Ross0907/pompyboard/pcb/pompyboard.kicad_sch

## KiCad design pcb/pompyboard.kicad_sch (2025-07-24)

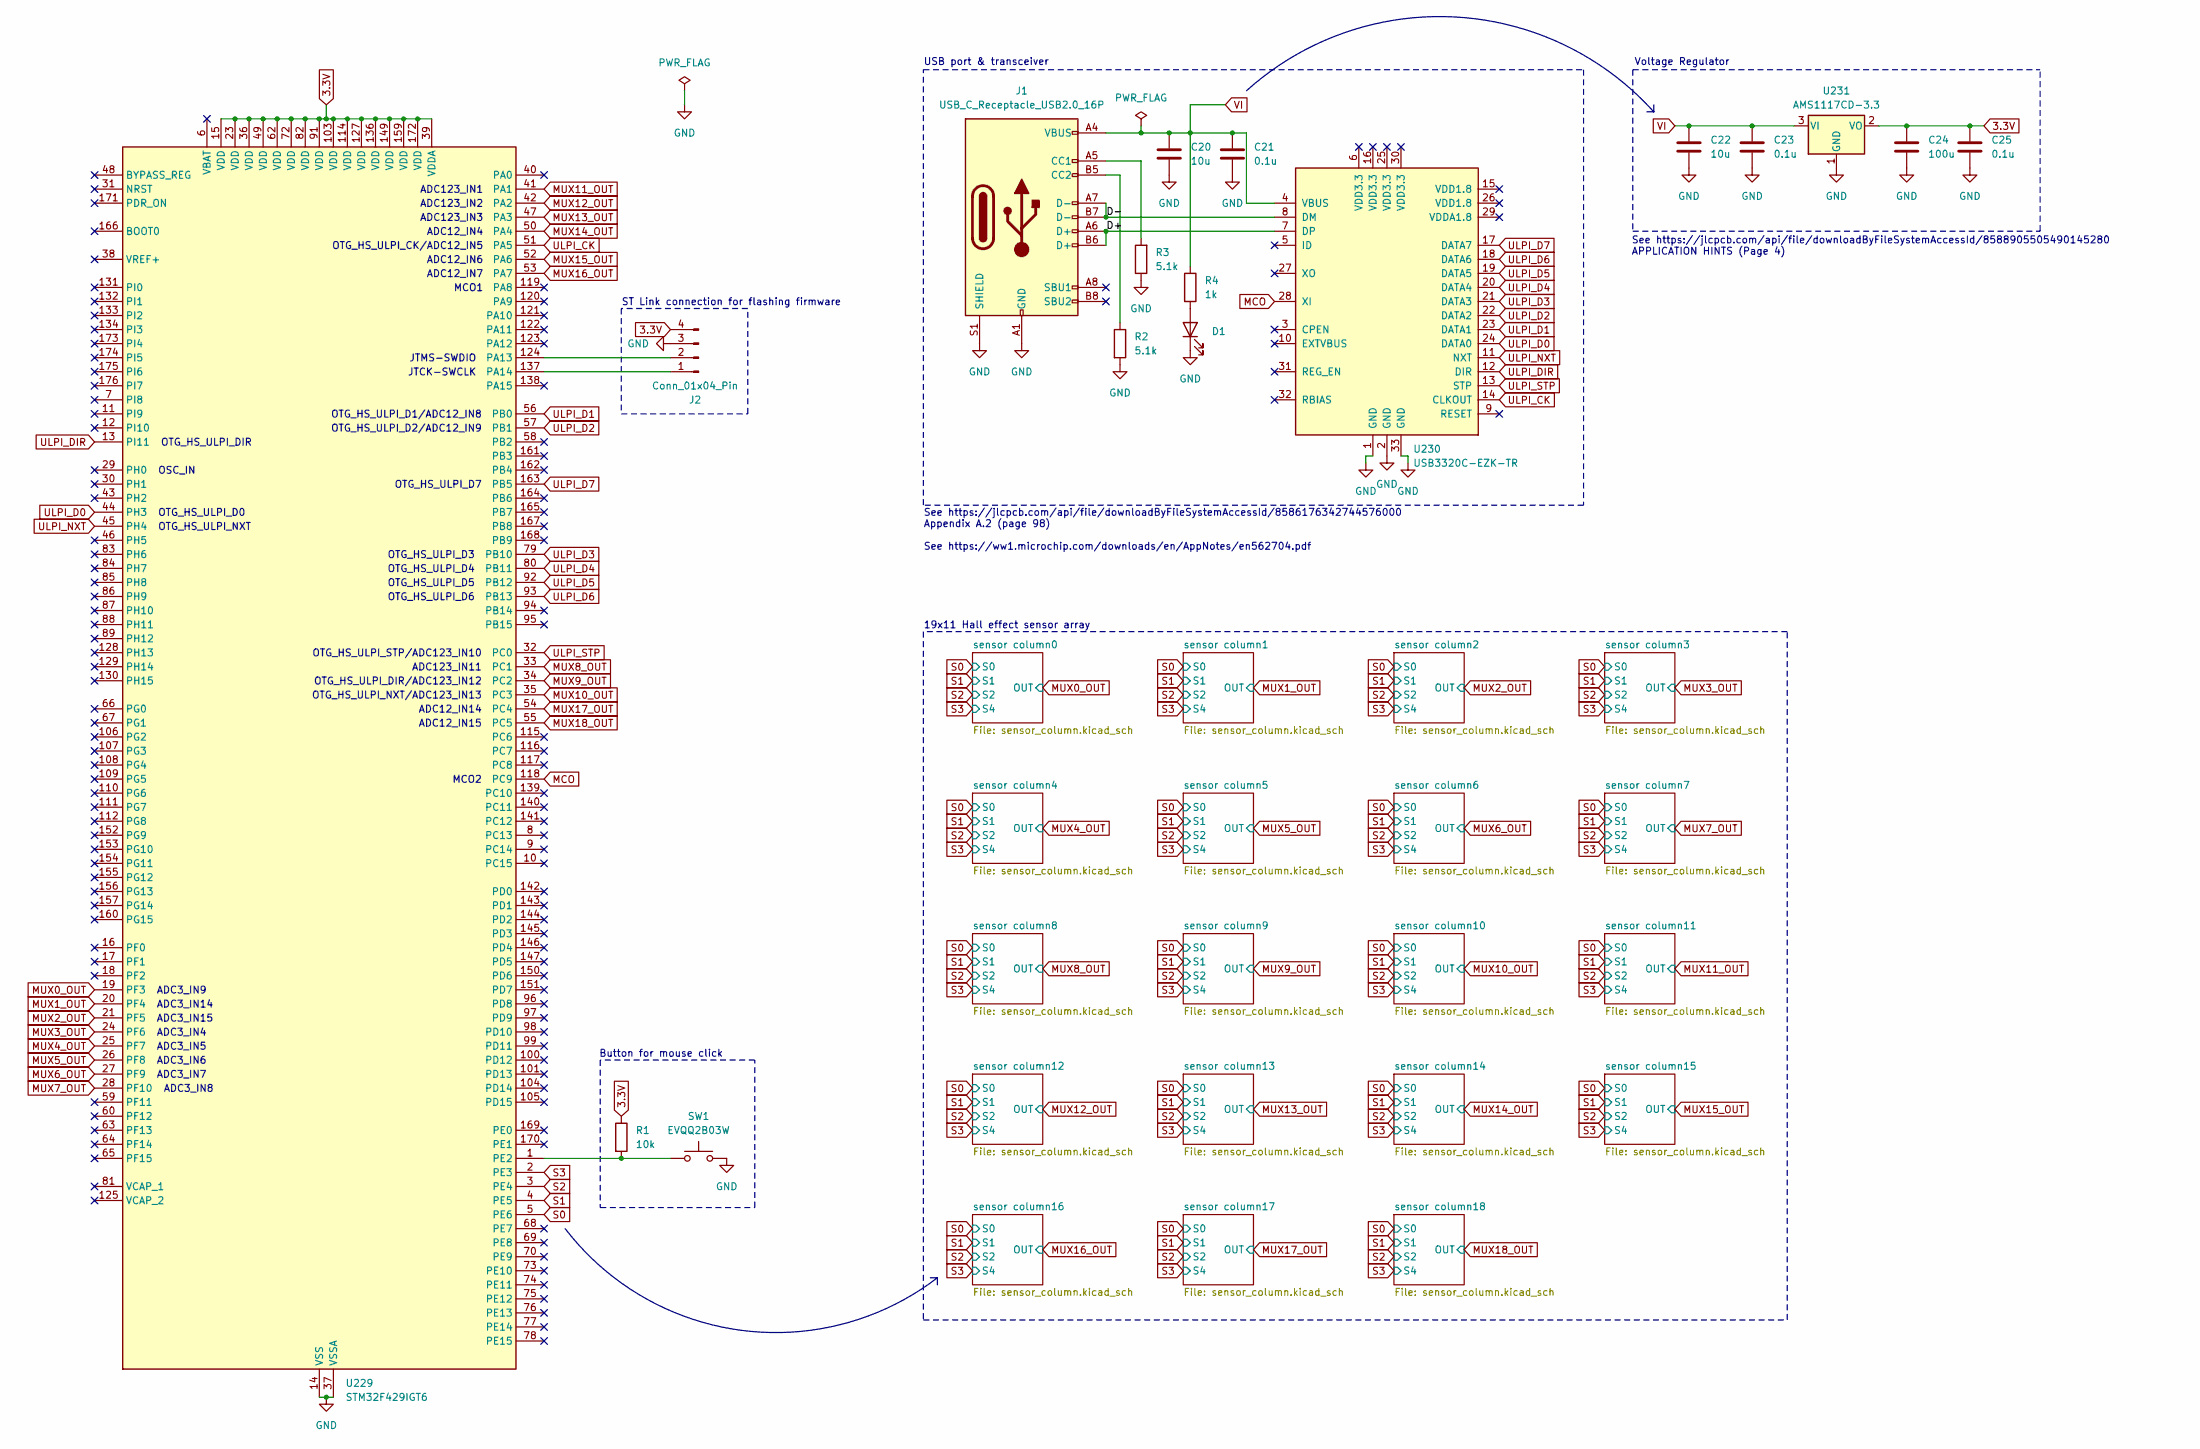
[picture p5: schematic pompyboard.kicad_sch]

Parts:
C20, C22: 10u; C_0603_1608Metric; LCSC Part # C19702
C21, C23, C25: 0.1u; C_0402_1005Metric; LCSC Part # C1525
C24: 100u; C_1206_3216Metric; LCSC Part # C6119960
D1: F.0603.00139/P2-0603R1TS2-06T-002; LED_0201_0603Metric; LCSC Part # C7496820
J1: USB_C_Receptacle_USB2.0_16P; USB_C_Receptacle_GCT_USB4085; LCSC Part # C7095263
J2: Conn_01x04_Pin; PinHeader_1x04_P2.54mm_Horizontal; LCSC Part # C32713263
R1: 10k; R_0402_1005Metric; LCSC Part # C25744
R2, R3: 5.1k; R_0402_1005Metric; LCSC Part # C25905
R4: 1k; R_0402_1005Metric; LCSC Part # C11702
SW1: EVQQ2B03W; SW_SPST_EVQQ2; LCSC Part # C79178
U229: STM32F429IGT6; LQFP-176_24x24mm_P0.5mm
U230: USB3320C-EZK-TR; QFN-32-1EP_5x5mm_P0.5mm_EP3.45x3.45mm
U231: AMS1117CD-3.3; TO-252-3_TabPin2

Connections:
3.3V: C24.1, C25.1, J2.4, R1.1, U229.15 (VDD), U229.23 (VDD), U229.36 (VDD), U229.39 (VDDA), U229.49 (VDD), U229.62 (VDD), U229.72 (VDD), U229.82 (VDD), U229.91 (VDD), U229.103 (VDD), U229.114 (VDD), U229.127 (VDD), U229.136 (VDD), U229.149 (VDD), U229.159 (VDD), U229.172 (VDD), U231.2 (VO)
D+: J1.A6 (D+), J1.B6 (D+), U230.7 (DP)
D-: J1.A7 (D-), J1.B7 (D-), U230.8 (DM)
GND: C20.2, C21.2, C22.2, C23.2, C24.2, C25.2, D1.1 (K), J1.A1 (GND), J1.A12 (GND), J1.B1 (GND), J1.B12 (GND), J1.S1 (SHIELD), J2.3, R2.2, R3.1, SW1.2, U229.14 (VSS), U229.22 (VSS), U229.37 (VSSA), U229.61 (VSS), U229.71 (VSS), U229.90 (VSS), U229.102 (VSS), U229.113 (VSS), U229.126 (VSS), U229.135 (VSS), U229.148 (VSS), U229.158 (VSS), U230.1 (GND), U230.2 (GND), U230.33 (GND), U231.1 (GND)
MCO: U229.118 (PC9), U230.28 (XI)
MUX0_OUT: U229.19 (PF3)
MUX1_OUT: U229.20 (PF4)
MUX2_OUT: U229.21 (PF5)
MUX3_OUT: U229.24 (PF6)
MUX4_OUT: U229.25 (PF7)
MUX5_OUT: U229.26 (PF8)
MUX6_OUT: U229.27 (PF9)
MUX7_OUT: U229.28 (PF10)
MUX8_OUT: U229.33 (PC1)
MUX9_OUT: U229.34 (PC2)
MUX10_OUT: U229.35 (PC3)
MUX11_OUT: U229.41 (PA1)
MUX12_OUT: U229.42 (PA2)
MUX13_OUT: U229.47 (PA3)
MUX14_OUT: U229.50 (PA4)
MUX15_OUT: U229.52 (PA6)
MUX16_OUT: U229.53 (PA7)
MUX17_OUT: U229.54 (PC4)
MUX18_OUT: U229.55 (PC5)
unnamed: D1.2 (A), R4.2
unnamed: J1.A5 (CC1), R3.2
unnamed: J1.B5 (CC2), R2.1
unnamed: J2.1, U229.137 (PA14)
unnamed: J2.2, U229.124 (PA13)
unnamed: R1.2, SW1.1, U229.1 (PE2)
S0: U229.5 (PE6)
S1: U229.4 (PE5)
S2: U229.3 (PE4)
S3: U229.2 (PE3)
ULPI_CK: U229.51 (PA5), U230.14 (CLKOUT)
ULPI_D0: U229.44 (PH3), U230.24 (DATA0)
ULPI_D1: U229.56 (PB0), U230.23 (DATA1)
ULPI_D2: U229.57 (PB1), U230.22 (DATA2)
ULPI_D3: U229.79 (PB10), U230.21 (DATA3)
ULPI_D4: U229.80 (PB11), U230.20 (DATA4)
ULPI_D5: U229.92 (PB12), U230.19 (DATA5)
ULPI_D6: U229.93 (PB13), U230.18 (DATA6)
ULPI_D7: U229.163 (PB5), U230.17 (DATA7)
ULPI_DIR: U229.13 (PI11), U230.12 (DIR)
ULPI_NXT: U229.45 (PH4), U230.11 (NXT)
ULPI_STP: U229.32 (PC0), U230.13 (STP)
VI: C20.1, C21.1, C22.1, C23.1, J1.A4 (VBUS), J1.A9 (VBUS), J1.B4 (VBUS), J1.B9 (VBUS), R4.1, U230.4 (VBUS), U231.3 (VI)

Notes on the sheet:
ADC3_IN6
ADC3_IN8
ADC12_IN15
OTG_HS_ULPI_D4
OTG_HS_ULPI_D7
ADC3_IN14
OTG_HS_ULPI_NXT
ADC12_IN14
OTG_HS_ULPI_STP/ADC123_IN10
OTG_HS_ULPI_DIR/ADC123_IN12
Button for mouse click
OTG_HS_ULPI_D2/ADC12_IN9
OTG_HS_ULPI_D3
ADC3_IN15
ADC3_IN4
ADC12_IN4
MCO2
Voltage Regulator
19x11 Hall effect sensor array
ADC3_IN9
See https://jlcpcb.com/api/file/downloadByFileSystemAccessId/8586176342744576000 Appendix A.2 (page 98) See https://ww1.microchip.com/downloads/en/AppNotes/en562704.pdf
ADC123_IN1
OTG_HS_ULPI_NXT/ADC123_IN13
ADC12_IN6
OSC_IN
ADC3_IN5
OTG_HS_ULPI_CK/ADC12_IN5
ST Link connection for flashing firmware
OTG_HS_ULPI_DIR
JTCK-SWCLK
USB port & transceiver
OTG_HS_ULPI_D0
See https://jlcpcb.com/api/file/downloadByFileSystemAccessId/8588905505490145280 APPLICATION HINTS (Page 4)
MCO1
OTG_HS_ULPI_D5
ADC123_IN11
OTG_HS_ULPI_D1/ADC12_IN8
ADC12_IN7
JTMS-SWDIO
OTG_HS_ULPI_D6
ADC123_IN3
ADC123_IN2
ADC3_IN7
