Ross0907/pompyboard/pcb/sensor_column.kicad_sch

## KiCad design pcb/sensor_column.kicad_sch (2025-07-24)

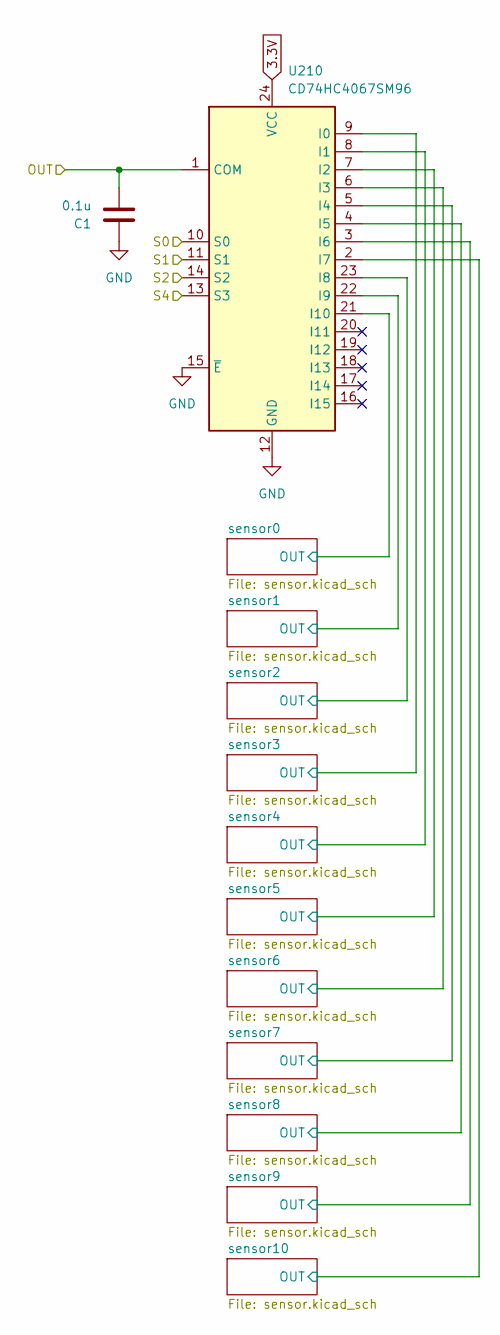
[picture p6: schematic sensor_column.kicad_sch]

Parts:
C1: 0.1u; C_0402_1005Metric; LCSC Part # C1525
U210: CD74HC4067SM96; SSOP-24_5.3x8.2mm_P0.65mm

Connections:
3.3V: U210.24 (VCC)
GND: C1.1, U210.12 (GND), U210.15 (~E)
OUT: C1.2, U210.1 (COM), U210.2 (I7), U210.3 (I6), U210.4 (I5), U210.5 (I4), U210.6 (I3), U210.7 (I2), U210.8 (I1), U210.9 (I0), U210.21 (I10), U210.22 (I9), U210.23 (I8)
S0: U210.10 (S0)
S1: U210.11 (S1)
S2: U210.14 (S2)
S4: U210.13 (S3)
